brunobpinto/Dancing-Robot/3D_Files/Adam_v2 Thigh Extension.SLDPRT

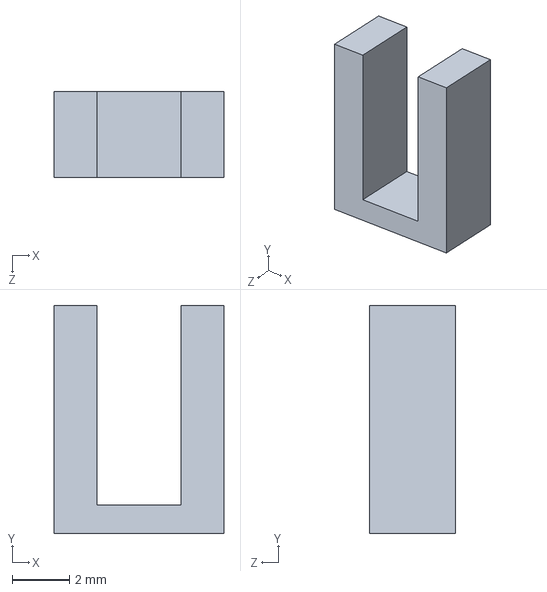
[picture p15: CAD file, 2024-12-12]
3D_Files/Adam_v2 Thigh Extension.SLDPRT
5.95 x 8.00 x 3.00 mm
