brunobpinto/Dancing-Robot/3D_Files/Adam_v1 Arm.SLDPRT

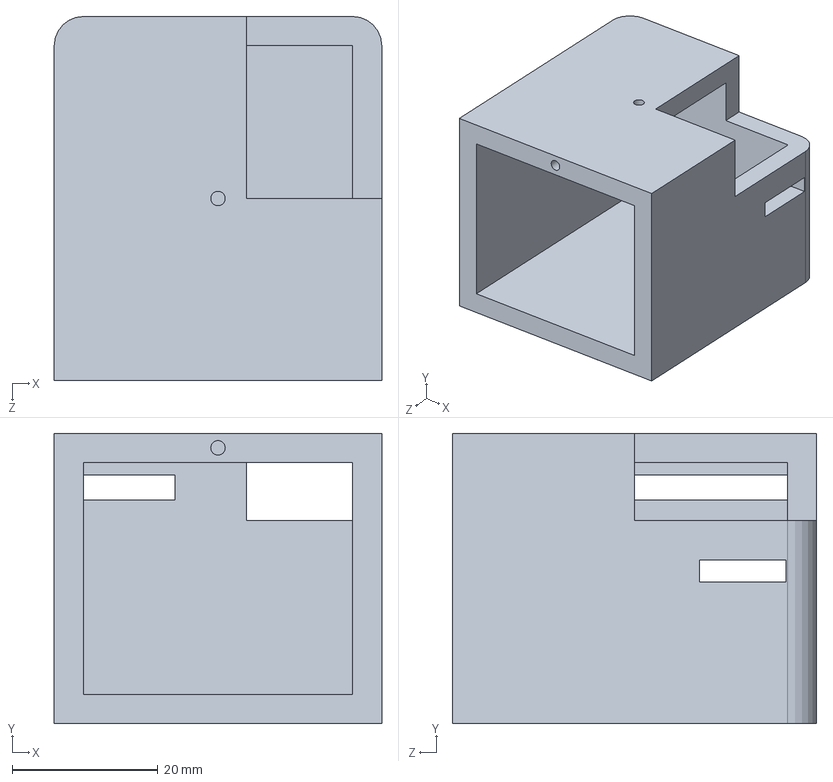
[picture p16: CAD file, 2024-12-12]
3D_Files/Adam_v1 Arm.SLDPRT
45.0 x 39.9 x 50.0 mm
