brunobpinto/Dancing-Robot/3D_Files/Adam_v1 Torso_Cap.SLDPRT

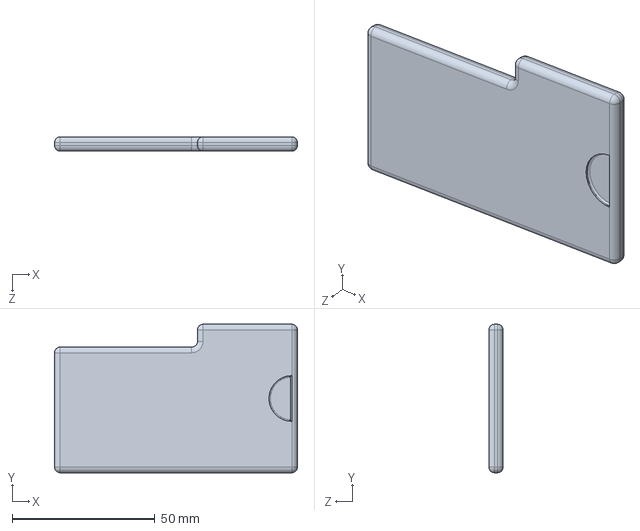
[picture p17: CAD file, 2024-12-12]
3D_Files/Adam_v1 Torso_Cap.SLDPRT
85.0 x 52.0 x 5.00 mm
