brunobpinto/Dancing-Robot/3D_Files/Adam_v1 Hip.SLDPRT

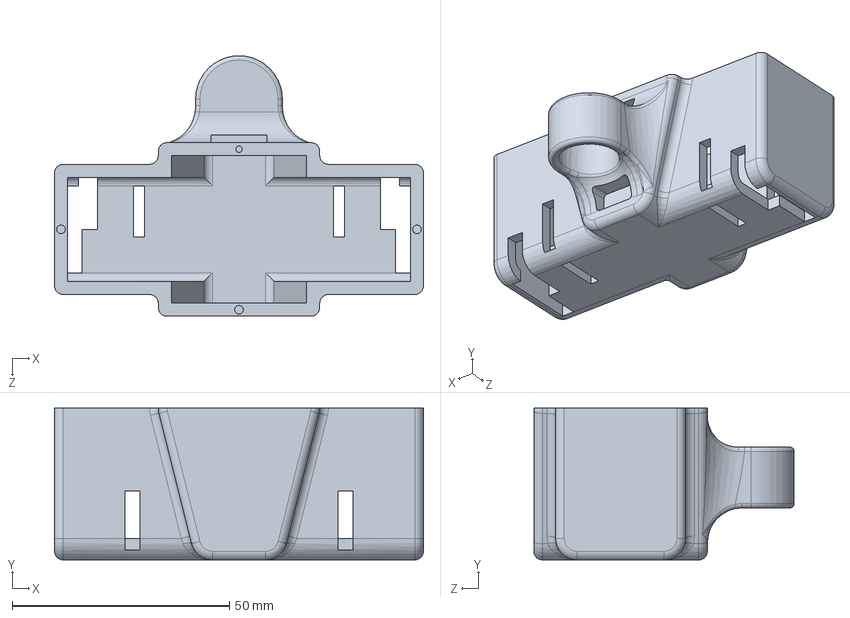
[picture p18: CAD file, 2024-12-12]
3D_Files/Adam_v1 Hip.SLDPRT
85.0 x 35.0 x 60.0 mm
