brunobpinto/Dancing-Robot/3D_Files/Adam_v1 Arm Extension.SLDPRT

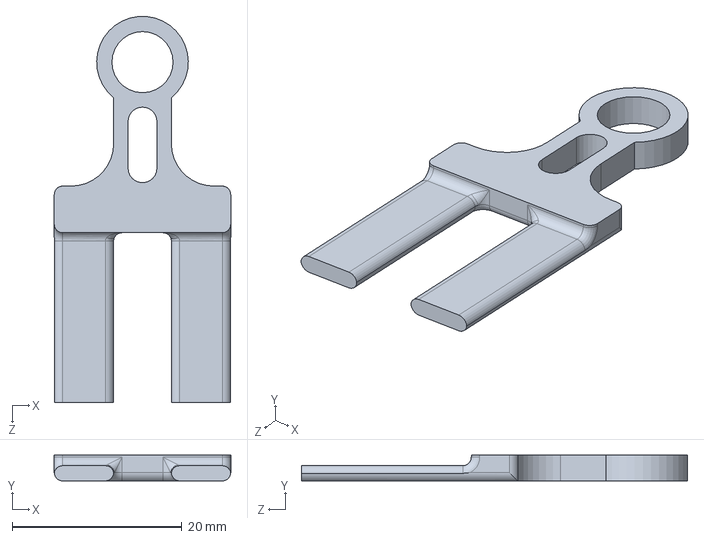
[picture p19: CAD file, 2024-12-12]
3D_Files/Adam_v1 Arm Extension.SLDPRT
20.8 x 3.05 x 45.5 mm
