brunobpinto/Dancing-Robot/3D_Files/Adam_v1 Head.SLDPRT

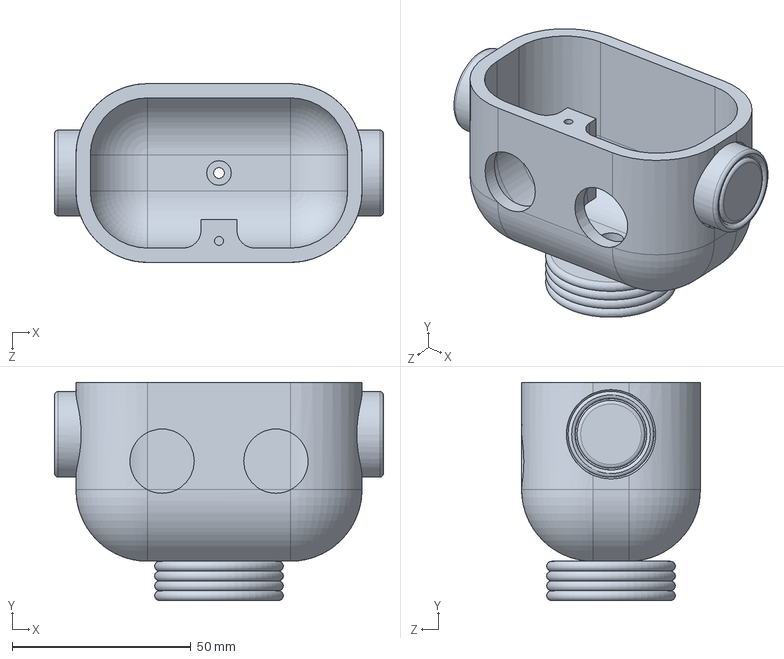
[picture p20: CAD file, 2024-12-12]
3D_Files/Adam_v1 Head.SLDPRT
92.0 x 61.0 x 50.0 mm
